a5632645/final_design/pctest/raylib/examples/audio/audio_mixed_processor.png

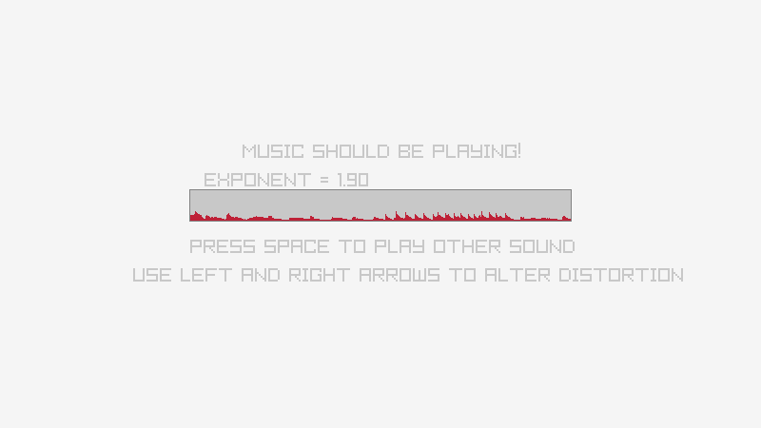
pctest/raylib/examples/audio/audio_mixed_processor.png
