a5632645/final_design/pctest/raylib/examples/audio/audio_stream_effects.png

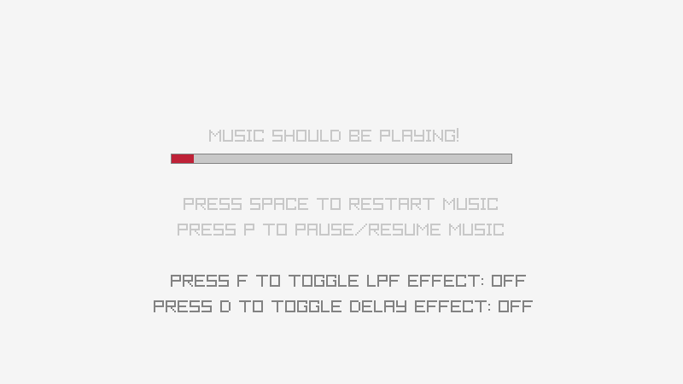
pctest/raylib/examples/audio/audio_stream_effects.png
