a5632645/final_design/pctest/raylib/examples/core/core_automation_events.png

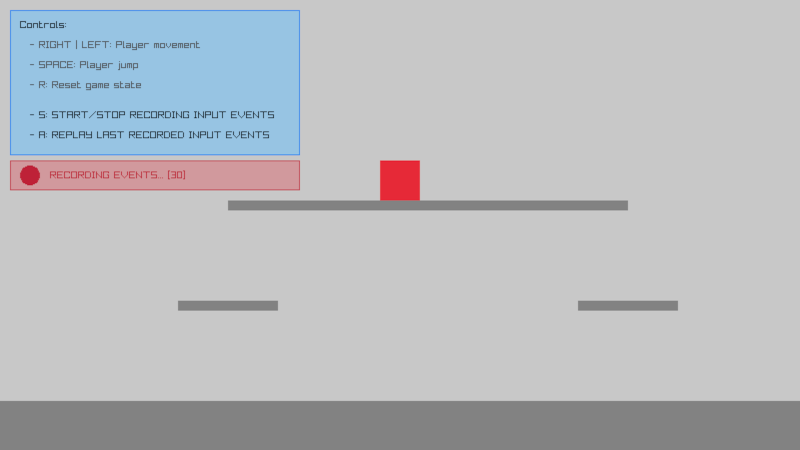
pctest/raylib/examples/core/core_automation_events.png
