a5632645/final_design/pctest/raylib/examples/core/core_input_gestures_web.png

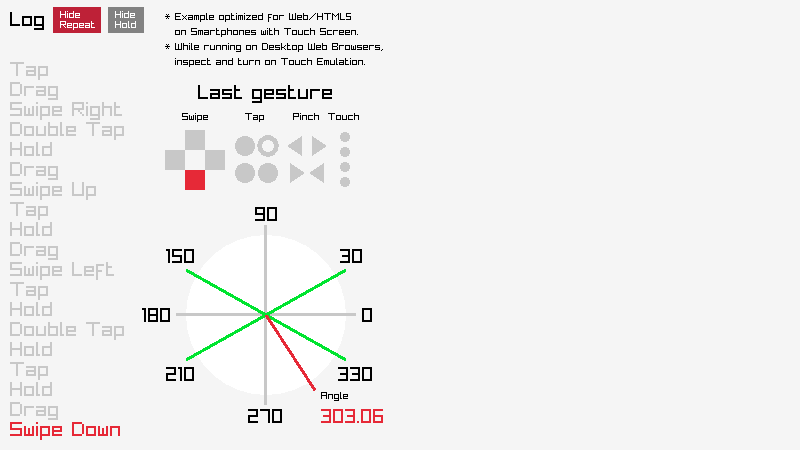
pctest/raylib/examples/core/core_input_gestures_web.png
