a5632645/final_design/pctest/raylib/examples/core/resources/ps3.png

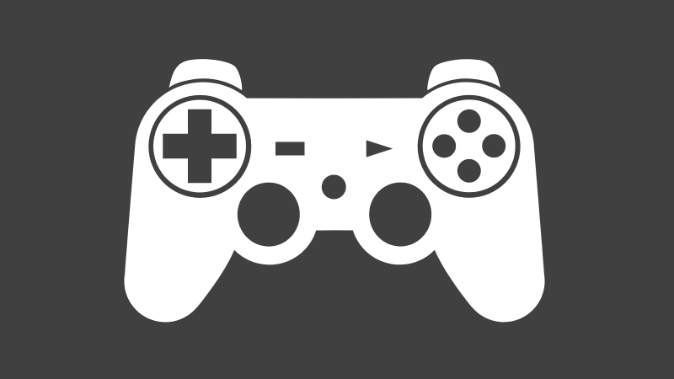
pctest/raylib/examples/core/resources/ps3.png
