a5632645/final_design/pctest/raylib/examples/core/resources/xbox.png

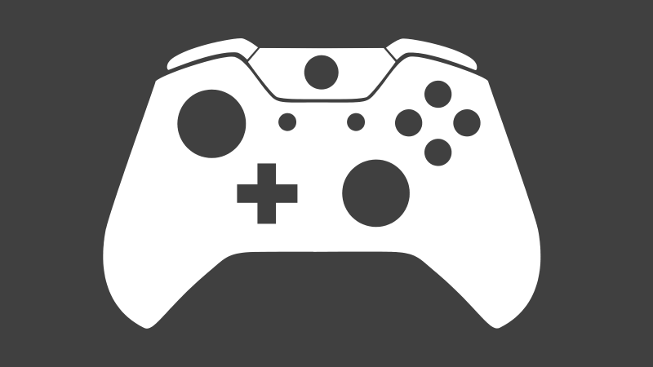
pctest/raylib/examples/core/resources/xbox.png
