a5632645/final_design/pctest/raylib/examples/models/models_bone_socket.png

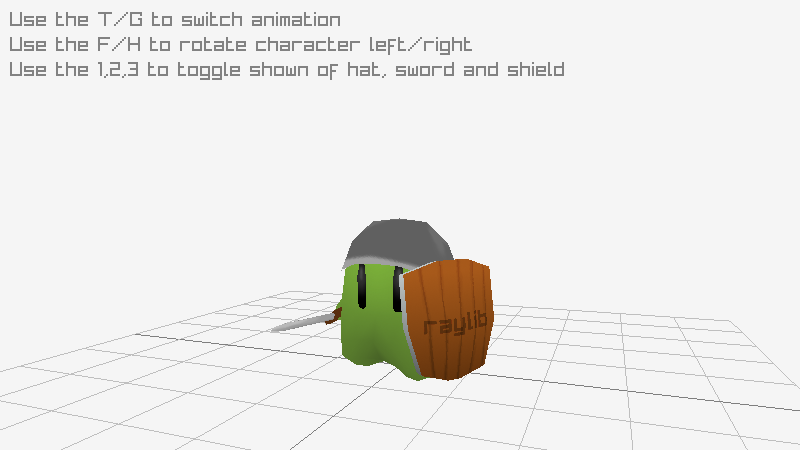
pctest/raylib/examples/models/models_bone_socket.png
