a5632645/final_design/pctest/raylib/examples/models/models_draw_cube_texture.png

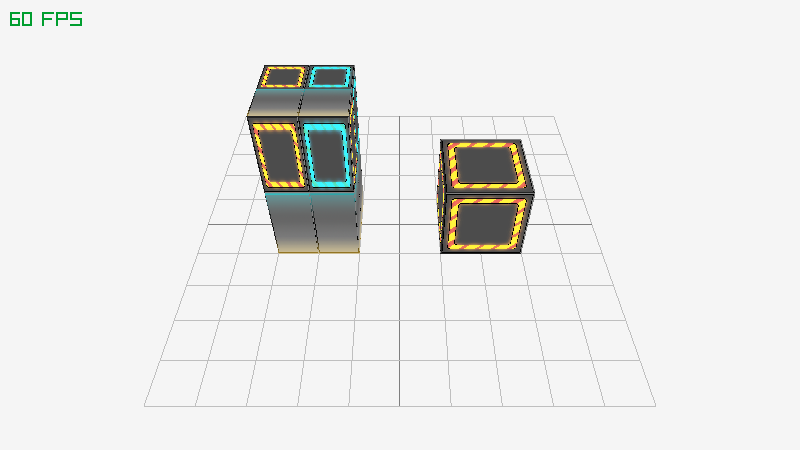
pctest/raylib/examples/models/models_draw_cube_texture.png
