a5632645/final_design/pctest/raylib/examples/models/resources/billboard.png

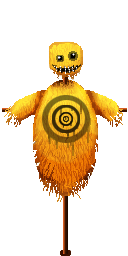
pctest/raylib/examples/models/resources/billboard.png
