a5632645/final_design/pctest/raylib/examples/models/resources/cubicmap_atlas.png

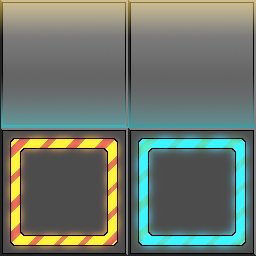
pctest/raylib/examples/models/resources/cubicmap_atlas.png
