a5632645/final_design/pctest/raylib/examples/models/resources/heightmap.png

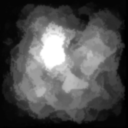
pctest/raylib/examples/models/resources/heightmap.png
