a5632645/final_design/pctest/raylib/examples/models/resources/models/iqm/guytex.png

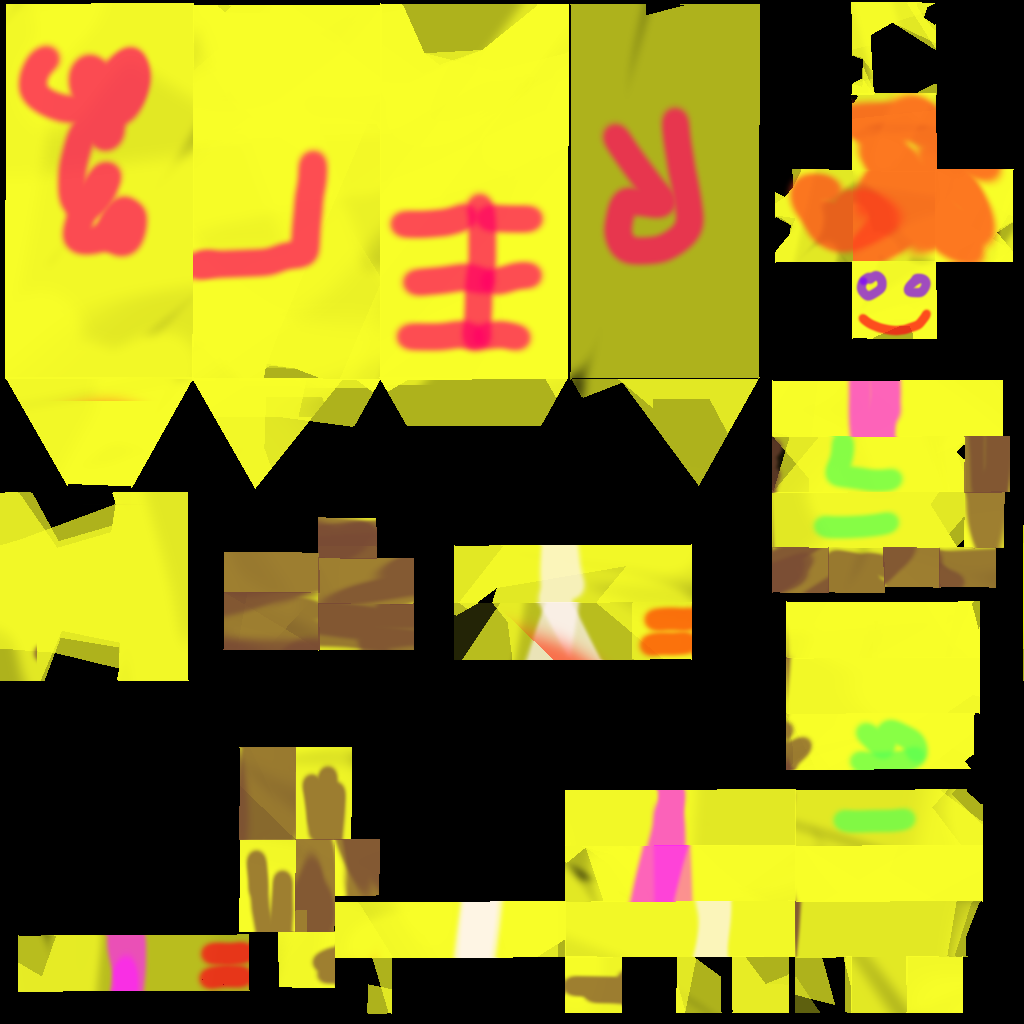
pctest/raylib/examples/models/resources/models/iqm/guytex.png
