a5632645/final_design/pctest/raylib/examples/models/resources/models/obj/castle_diffuse.png

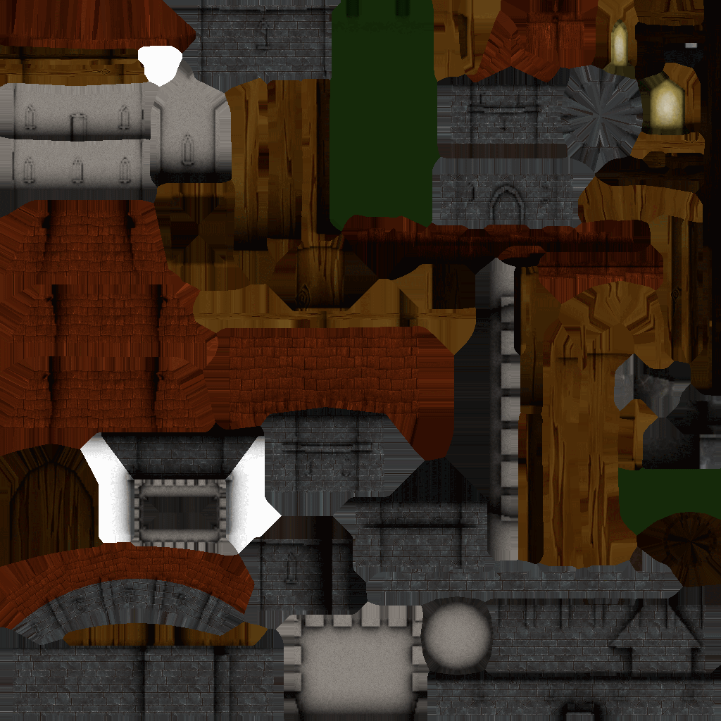
pctest/raylib/examples/models/resources/models/obj/castle_diffuse.png
