a5632645/final_design/pctest/raylib/examples/models/resources/models/obj/cube_diffuse.png

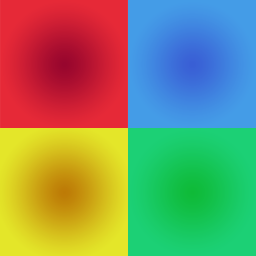
pctest/raylib/examples/models/resources/models/obj/cube_diffuse.png
