a5632645/final_design/pctest/raylib/examples/models/resources/models/obj/well_diffuse.png

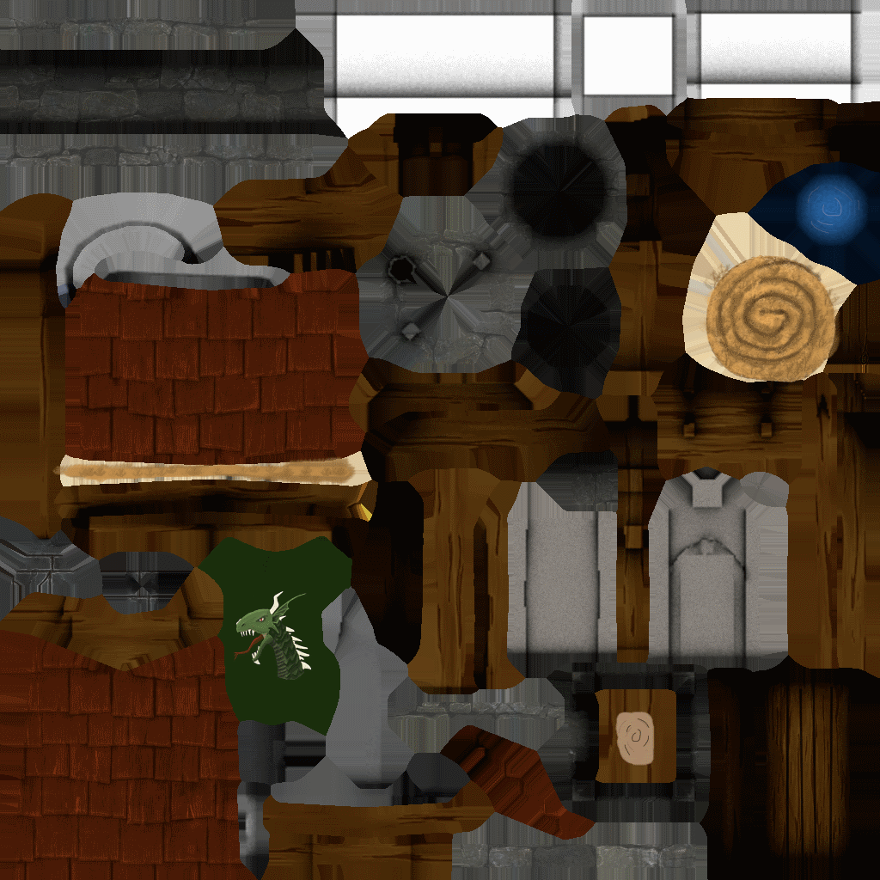
pctest/raylib/examples/models/resources/models/obj/well_diffuse.png
