a5632645/final_design/pctest/raylib/examples/models/resources/skybox.png

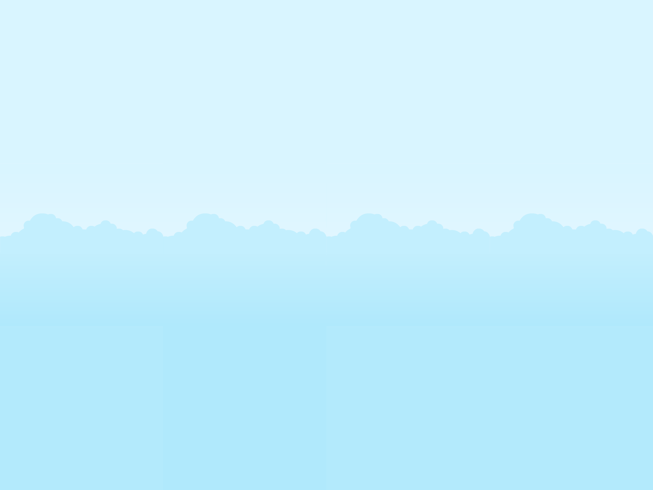
pctest/raylib/examples/models/resources/skybox.png
