a5632645/final_design/pctest/raylib/examples/others/raymath_vector_angle.png

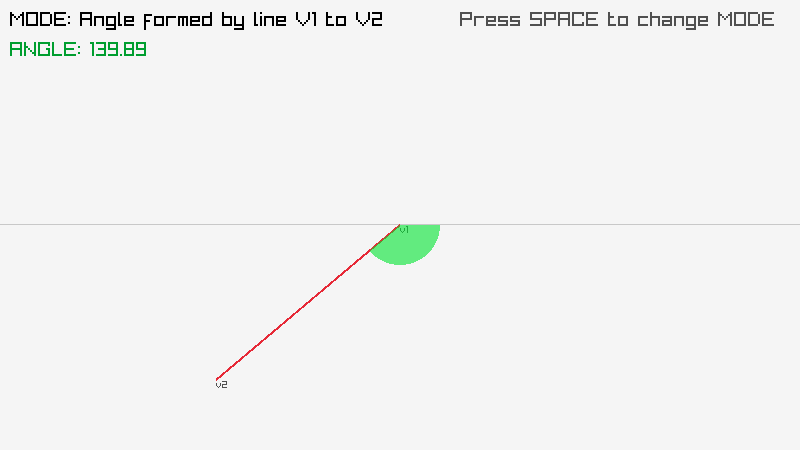
pctest/raylib/examples/others/raymath_vector_angle.png
