a5632645/final_design/pctest/raylib/examples/shaders/resources/fudesumi.png

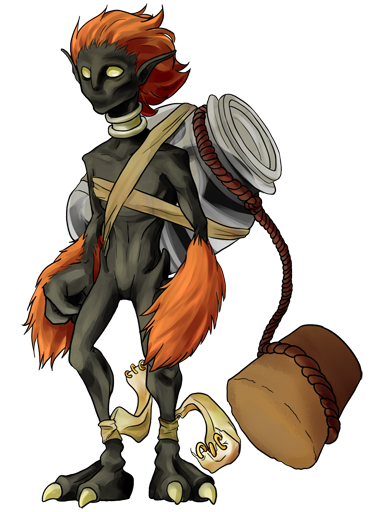
pctest/raylib/examples/shaders/resources/fudesumi.png
