a5632645/final_design/pctest/raylib/examples/shaders/resources/mask.png

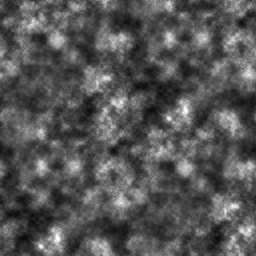
pctest/raylib/examples/shaders/resources/mask.png
