a5632645/final_design/pctest/raylib/examples/shaders/resources/models/barracks_diffuse.png

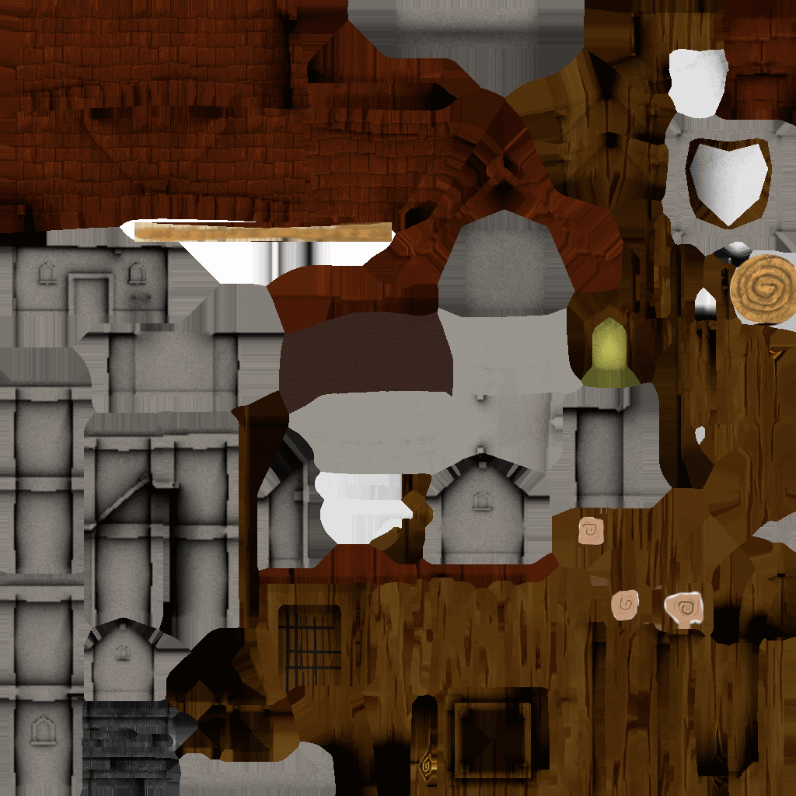
pctest/raylib/examples/shaders/resources/models/barracks_diffuse.png
