a5632645/final_design/pctest/raylib/examples/shaders/resources/models/watermill_diffuse.png

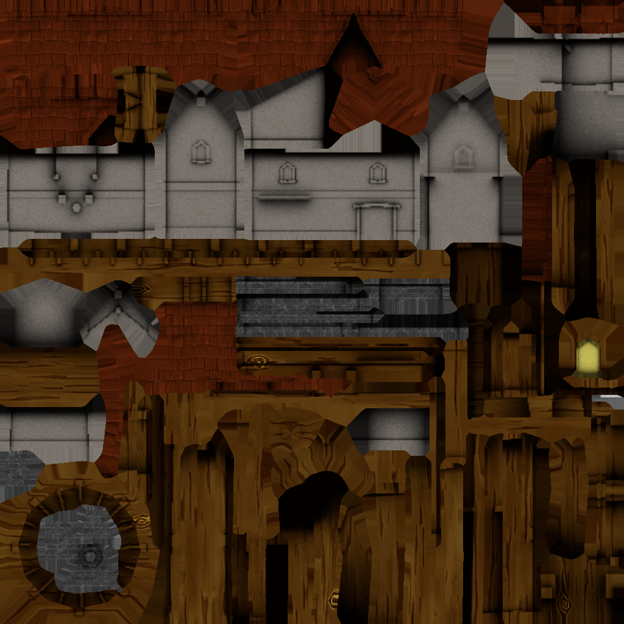
pctest/raylib/examples/shaders/resources/models/watermill_diffuse.png
