a5632645/final_design/pctest/raylib/examples/shaders/resources/plasma.png

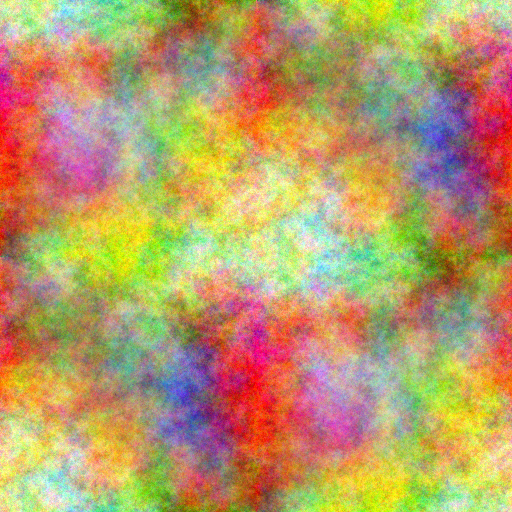
pctest/raylib/examples/shaders/resources/plasma.png
