a5632645/final_design/pctest/raylib/examples/shaders/resources/road_a.png

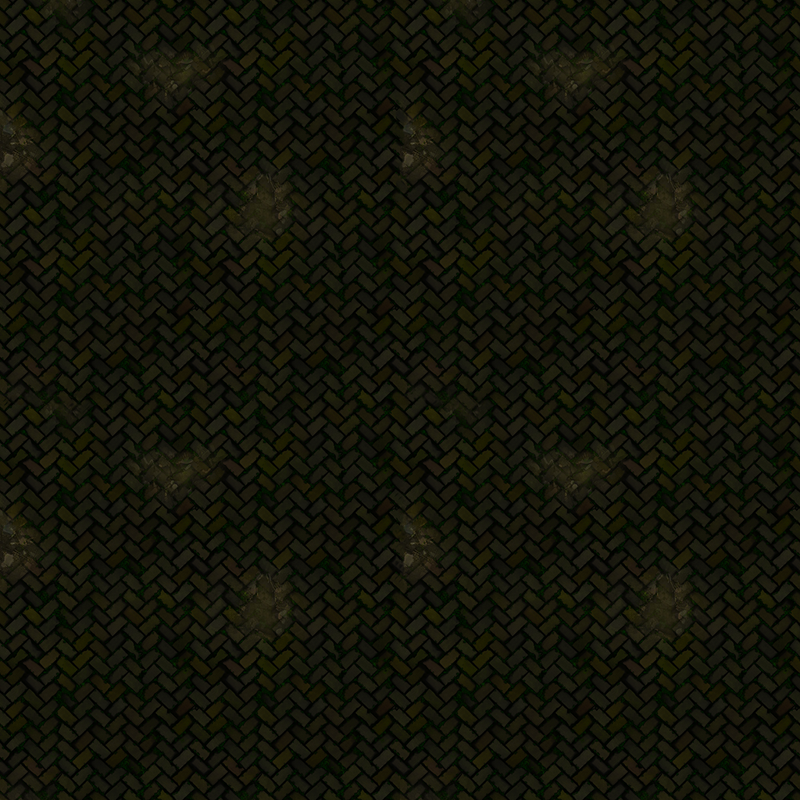
pctest/raylib/examples/shaders/resources/road_a.png
