a5632645/final_design/pctest/raylib/examples/shaders/resources/road_mra.png

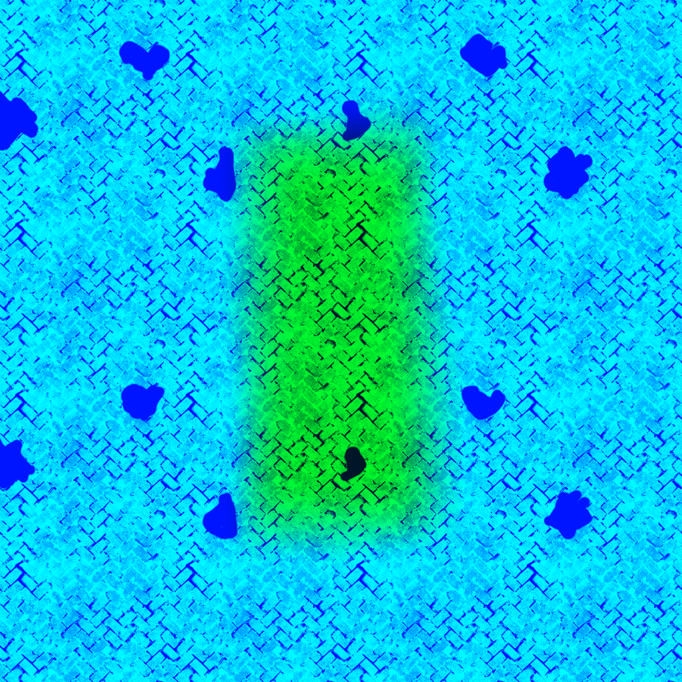
pctest/raylib/examples/shaders/resources/road_mra.png
