a5632645/final_design/pctest/raylib/examples/shaders/resources/road_n.png

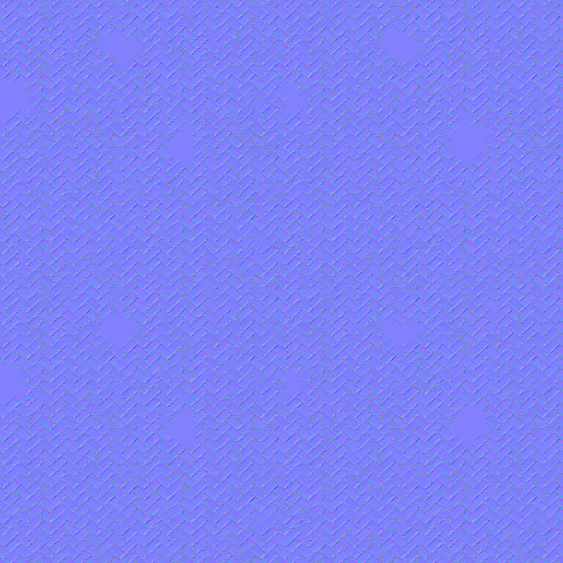
pctest/raylib/examples/shaders/resources/road_n.png
