a5632645/final_design/pctest/raylib/examples/shaders/resources/space.png

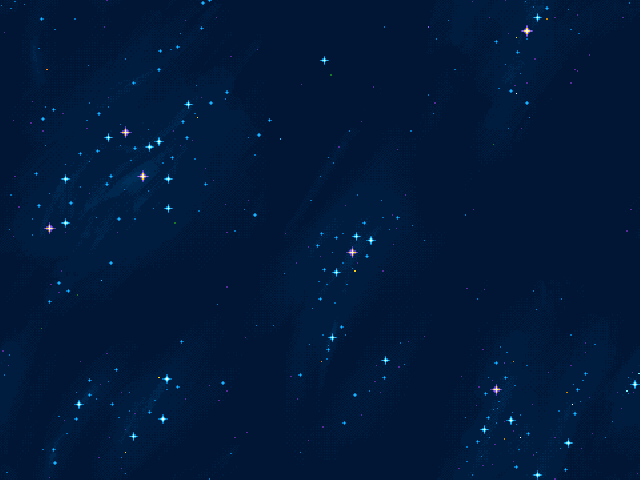
pctest/raylib/examples/shaders/resources/space.png
