a5632645/final_design/pctest/raylib/examples/shaders/resources/spark_flame.png

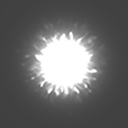
pctest/raylib/examples/shaders/resources/spark_flame.png
