a5632645/final_design/pctest/raylib/examples/shaders/resources/texel_checker.png

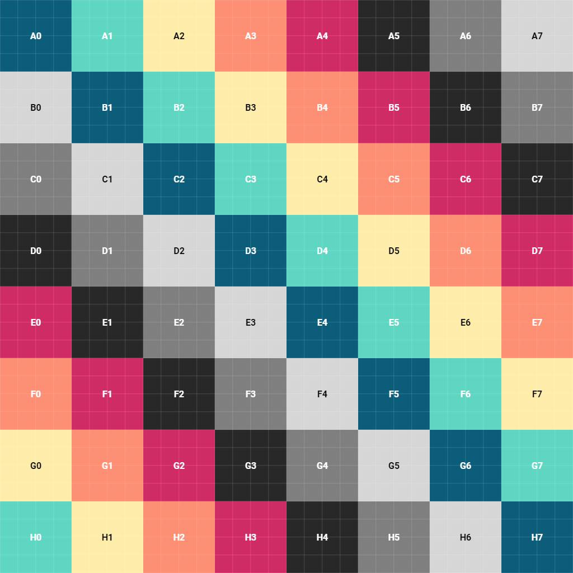
pctest/raylib/examples/shaders/resources/texel_checker.png
