a5632645/final_design/pctest/raylib/examples/shaders/shaders_basic_pbr.png

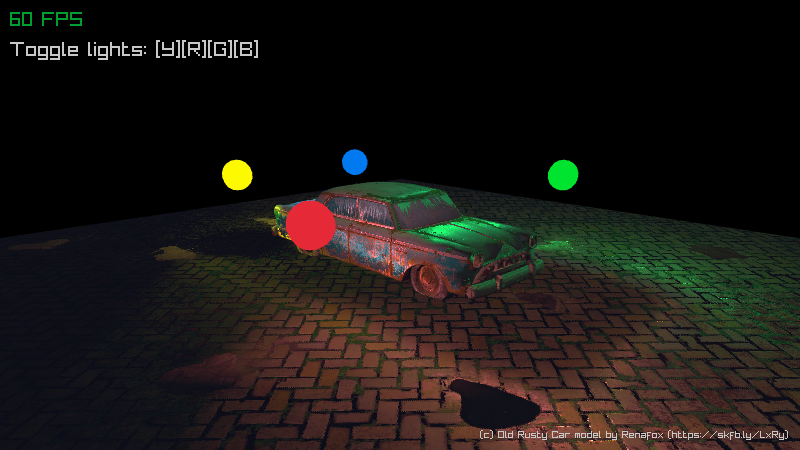
pctest/raylib/examples/shaders/shaders_basic_pbr.png
