a5632645/final_design/pctest/raylib/examples/shaders/shaders_hybrid_render.png

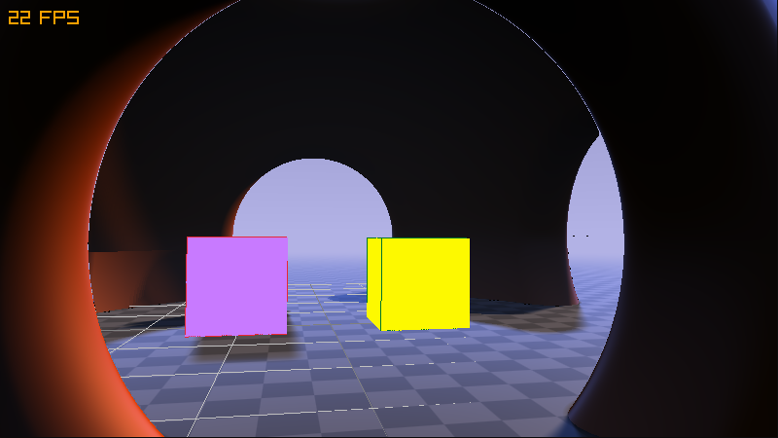
pctest/raylib/examples/shaders/shaders_hybrid_render.png
