a5632645/final_design/pctest/raylib/examples/shaders/shaders_lightmap.png

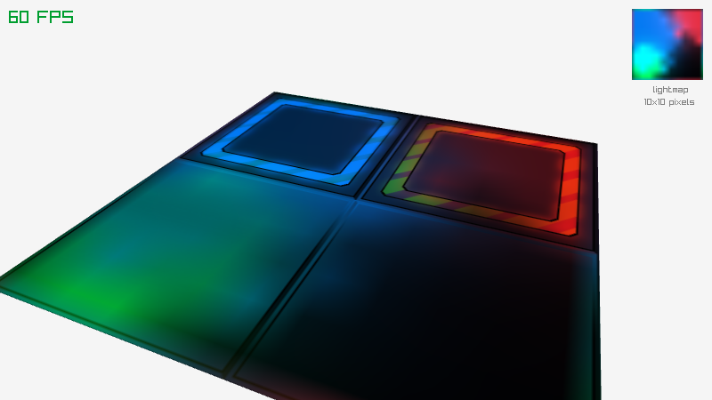
pctest/raylib/examples/shaders/shaders_lightmap.png
