a5632645/final_design/pctest/raylib/examples/shaders/shaders_shadowmap.png

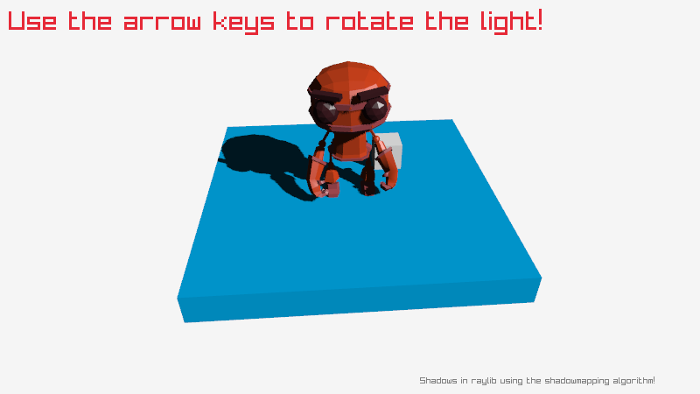
pctest/raylib/examples/shaders/shaders_shadowmap.png
