a5632645/final_design/pctest/raylib/examples/shaders/shaders_texture_tiling.png

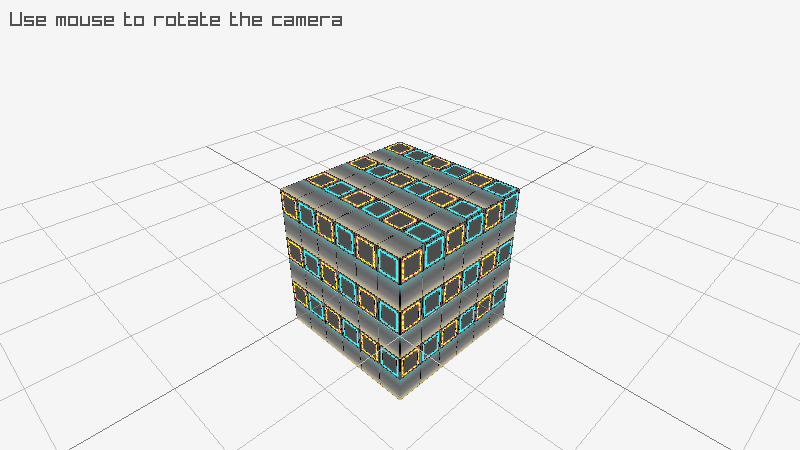
pctest/raylib/examples/shaders/shaders_texture_tiling.png
