a5632645/final_design/pctest/raylib/examples/shaders/shaders_vertex_displacement.png

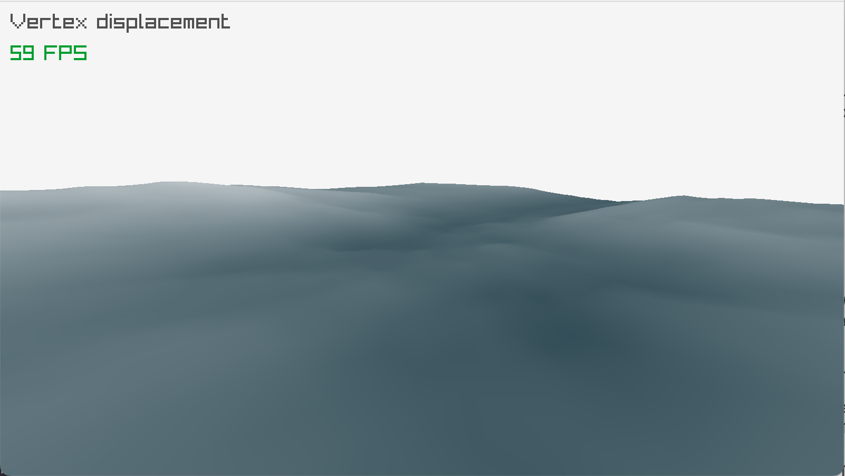
pctest/raylib/examples/shaders/shaders_vertex_displacement.png
