a5632645/final_design/pctest/raylib/examples/shaders/shaders_write_depth.png

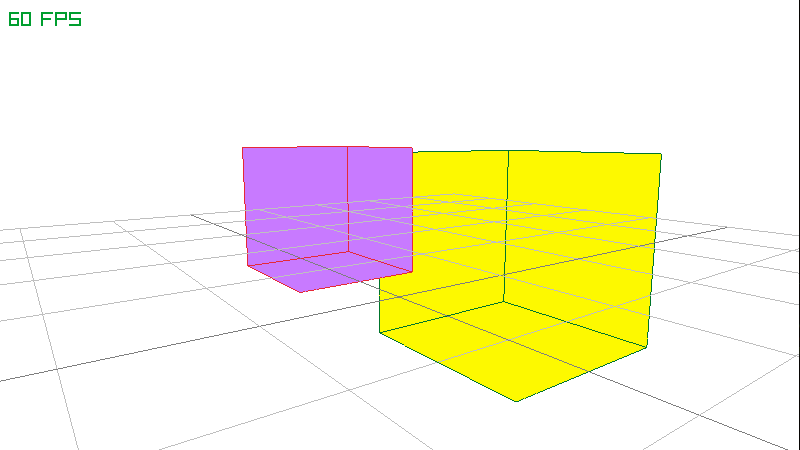
pctest/raylib/examples/shaders/shaders_write_depth.png
