a5632645/final_design/pctest/raylib/examples/shapes/shapes_splines_drawing.png

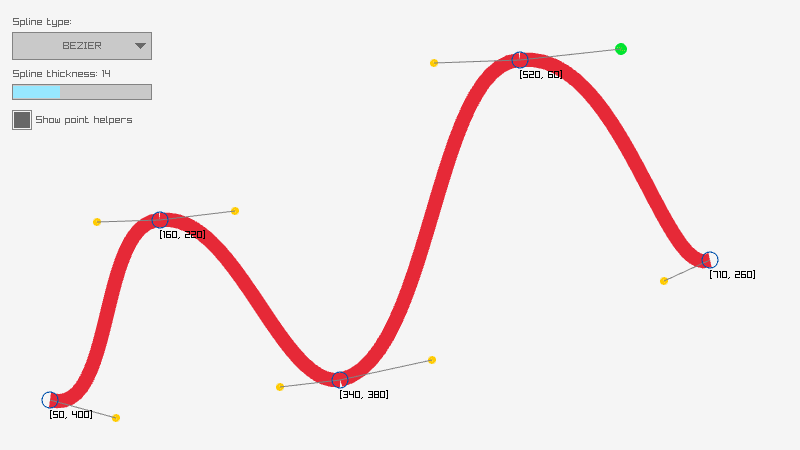
pctest/raylib/examples/shapes/shapes_splines_drawing.png
