a5632645/final_design/pctest/raylib/examples/text/resources/custom_alagard.png

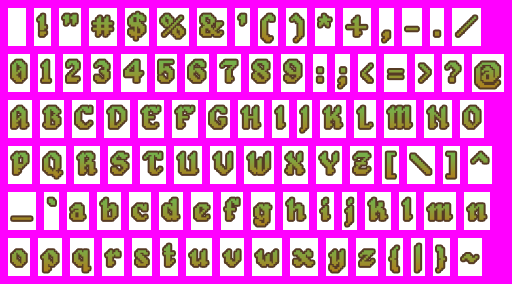
pctest/raylib/examples/text/resources/custom_alagard.png
