a5632645/final_design/pctest/raylib/examples/text/resources/custom_jupiter_crash.png

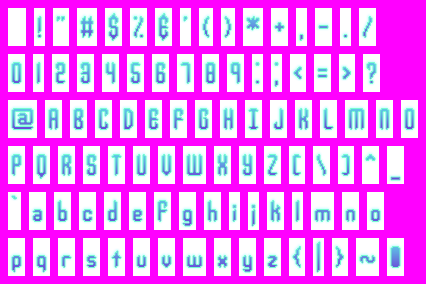
pctest/raylib/examples/text/resources/custom_jupiter_crash.png
