a5632645/final_design/pctest/raylib/examples/text/resources/custom_mecha.png

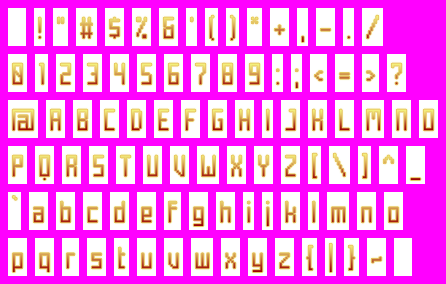
pctest/raylib/examples/text/resources/custom_mecha.png
