a5632645/final_design/pctest/raylib/examples/text/resources/dejavu.png

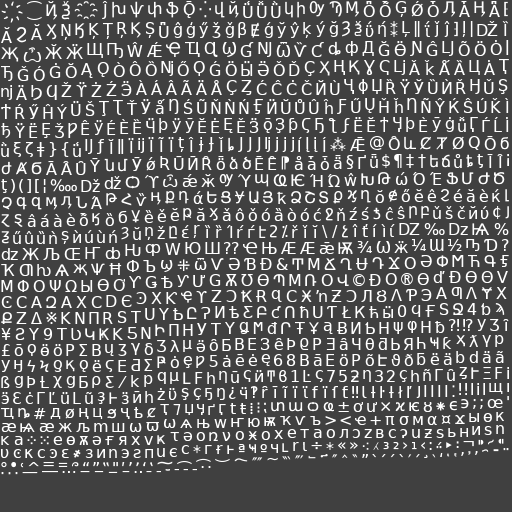
pctest/raylib/examples/text/resources/dejavu.png
