a5632645/final_design/pctest/raylib/examples/text/resources/fonts/alpha_beta.png

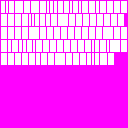
pctest/raylib/examples/text/resources/fonts/alpha_beta.png
