a5632645/final_design/pctest/raylib/examples/text/resources/fonts/jupiter_crash.png

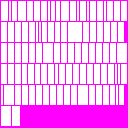
pctest/raylib/examples/text/resources/fonts/jupiter_crash.png
