a5632645/final_design/pctest/raylib/examples/text/resources/fonts/mecha.png

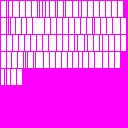
pctest/raylib/examples/text/resources/fonts/mecha.png
