a5632645/final_design/pctest/raylib/examples/text/resources/fonts/pixantiqua.png

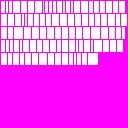
pctest/raylib/examples/text/resources/fonts/pixantiqua.png
