a5632645/final_design/pctest/raylib/examples/text/resources/fonts/pixelplay.png

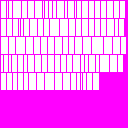
pctest/raylib/examples/text/resources/fonts/pixelplay.png
