a5632645/final_design/pctest/raylib/examples/text/resources/fonts/setback.png

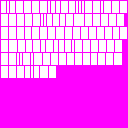
pctest/raylib/examples/text/resources/fonts/setback.png
