a5632645/final_design/pctest/raylib/examples/text/resources/noto_cjk.png

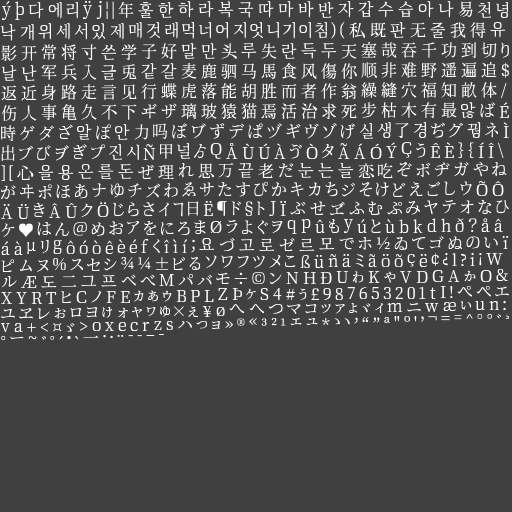
pctest/raylib/examples/text/resources/noto_cjk.png
