a5632645/final_design/pctest/raylib/examples/text/resources/pixantiqua.png

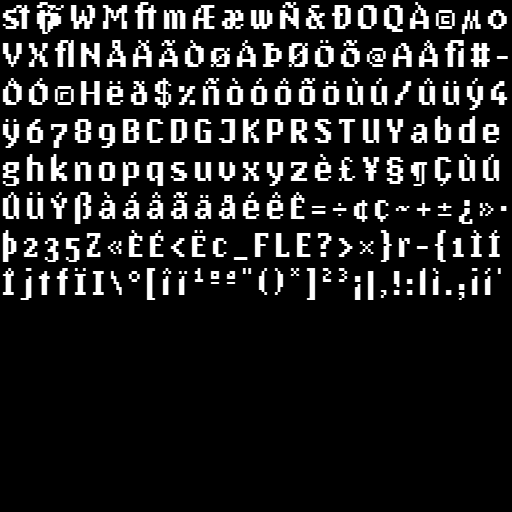
pctest/raylib/examples/text/resources/pixantiqua.png
