a5632645/final_design/pctest/raylib/examples/text/resources/symbola.png

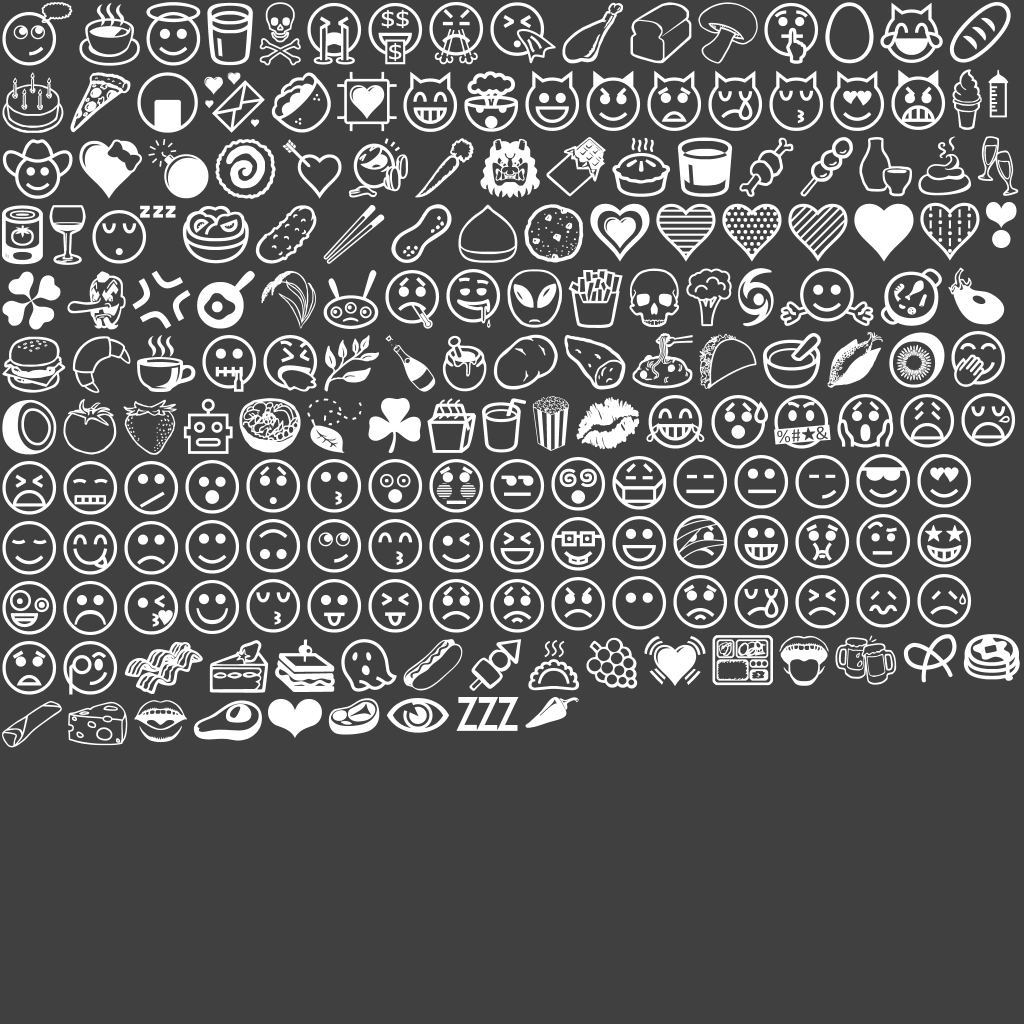
pctest/raylib/examples/text/resources/symbola.png
