a5632645/final_design/pctest/raylib/examples/textures/resources/button.png

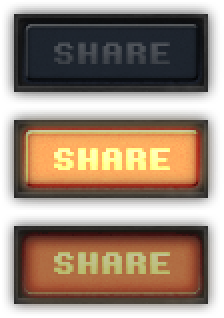
pctest/raylib/examples/textures/resources/button.png
