a5632645/final_design/pctest/raylib/examples/textures/resources/cat.png

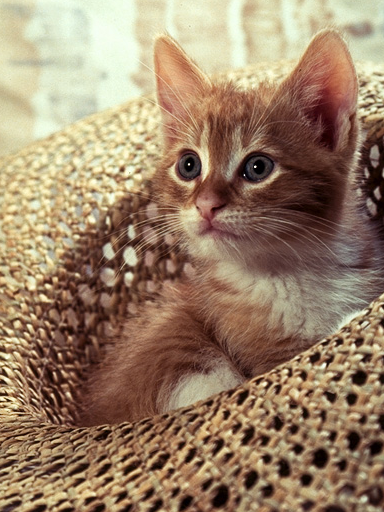
pctest/raylib/examples/textures/resources/cat.png
