a5632645/final_design/pctest/raylib/examples/textures/resources/cyberpunk_street_background.png

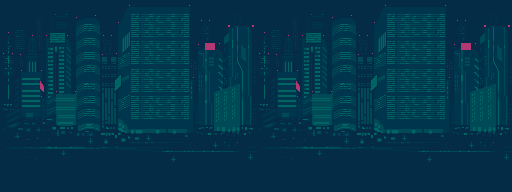
pctest/raylib/examples/textures/resources/cyberpunk_street_background.png
