a5632645/final_design/pctest/raylib/examples/textures/resources/cyberpunk_street_midground.png

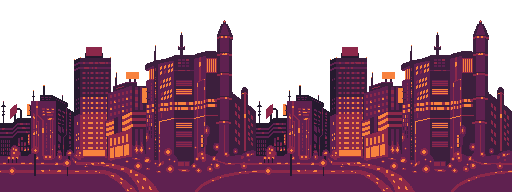
pctest/raylib/examples/textures/resources/cyberpunk_street_midground.png
