a5632645/final_design/pctest/raylib/examples/textures/resources/explosion.png

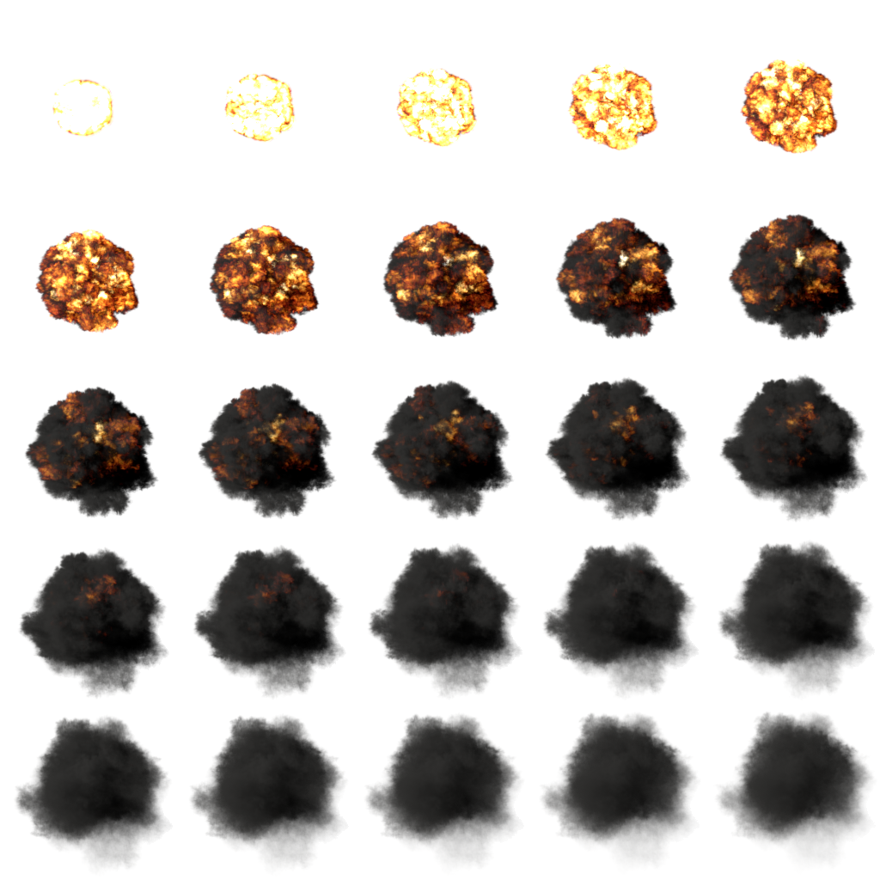
pctest/raylib/examples/textures/resources/explosion.png
