a5632645/final_design/pctest/raylib/examples/textures/resources/parrots.png

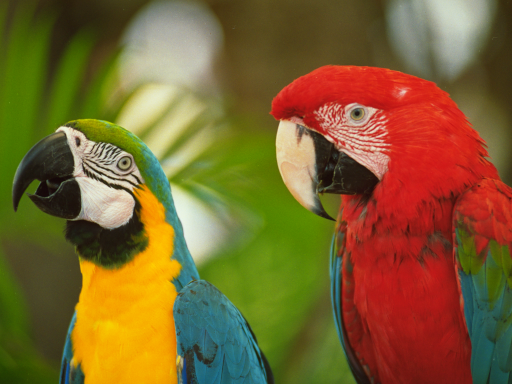
pctest/raylib/examples/textures/resources/parrots.png
