a5632645/final_design/pctest/raylib/examples/textures/resources/patterns.png

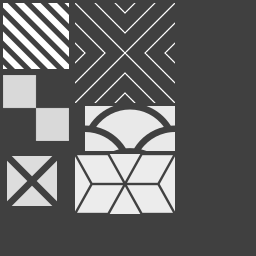
pctest/raylib/examples/textures/resources/patterns.png
