a5632645/final_design/pctest/raylib/examples/textures/resources/scarfy_run.gif

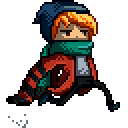
pctest/raylib/examples/textures/resources/scarfy_run.gif
