a5632645/final_design/pctest/raylib/examples/textures/textures_image_rotate.png

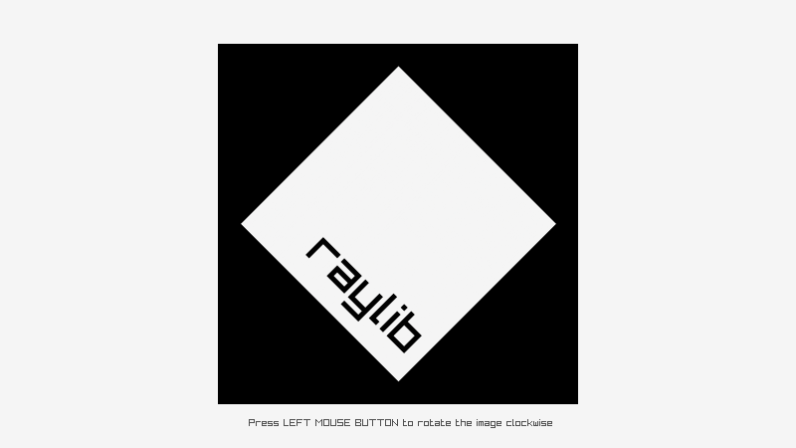
pctest/raylib/examples/textures/textures_image_rotate.png
