a5632645/final_design/pctest/raylib/examples/textures/textures_textured_curve.png

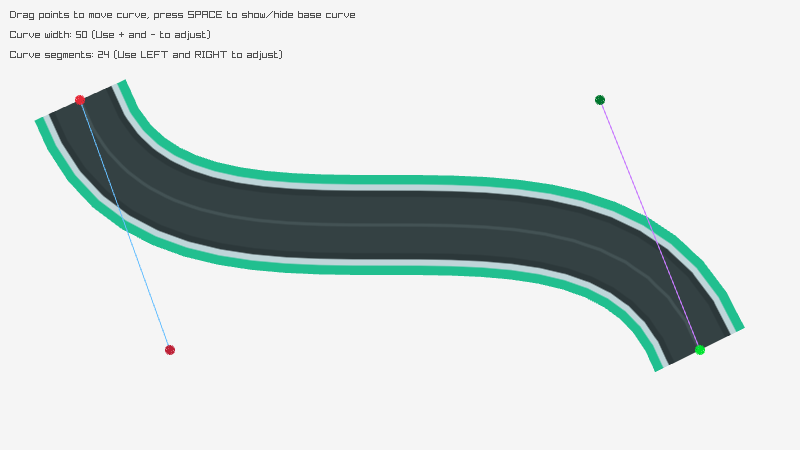
pctest/raylib/examples/textures/textures_textured_curve.png
