a5632645/final_design/WaveGuideSoft/CMSIS-DSP-1.16.2/Documentation/Doxygen/src/images/CFFT_Radix2.gif

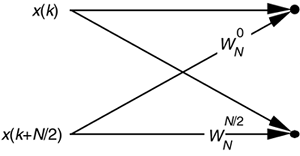
WaveGuideSoft/CMSIS-DSP-1.16.2/Documentation/Doxygen/src/images/CFFT_Radix2.gif
