a5632645/final_design/WaveGuideSoft/Waveguide/dsp/Body.cpp

#include "Body.hpp"
#include "AudioFFT.h"
#include <numbers>
#include <cmath>
#include "utli/Lerp.hpp"
#include "MemAttributes.hpp"

constexpr float kBanjo[4096] = {0.8408116, -0.2511731, -0.38303635, -0.0059898444, -0.27061847, 0.0007890034, -0.0073292973, 0.011994778, -0.012411621, 0.04655279, 0.056455344, 0.014067898, 0.07330127, -0.05343846, 0.028716885, -0.010607676, 0.0015999887, 0.043362975, -0.032687552, 0.0154145565, 0.062117293, 0.025567032, -0.08403967, 0.0062902574, 0.010043268, -0.051865425, 0.033150233, 0.020506015, -0.0044696927, 0.04990088, 0.03276305, -0.04390349, -0.02187753, -0.046611894, -0.07722027, -0.027850313, 0.01636171, 0.0030558843, -0.032876786, -0.036291096, -0.09235733, -0.087776974, -0.03540004, -0.04335503, -0.0653021, -0.044091616, -0.107368715, -0.19948685, -0.12446984, -0.12928312, -0.17091624, -0.15268704, -0.16255362, -0.12987855, -0.069635436, -0.060110703, -0.1134893, -0.11407602, -0.12384962, -0.09637414, -0.044933986, -0.07018676, -0.036956374, -0.034364752, -0.018860595, 0.025873553, 0.02347859, 0.0366431, 0.016929181, 0.038740564, 0.094063744, 0.10979407, 0.07708771, 0.040532988, 0.055806838, 0.06596992, 0.08629575, 0.13908072, 0.21054052, 0.19513358, 0.1566528, 0.15990843, 0.11960288, 0.16314034, 0.22333363, 0.2422042, 0.2616581, 0.27669352, 0.31851187, 0.29176015, 0.22406402, 0.15822846, 0.1264795, 0.12470437, 0.11616462, 0.10107283, 0.073159724, 0.1277734, 0.175093, 0.14201444, 0.07894555, 0.023511363, 0.012008642, -0.015200933, -0.030257491, -0.047351334, -0.07098553, -0.05507381, -0.0735658, -0.12708904, -0.17628899, -0.20585562, -0.21016774, -0.21126585, -0.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
