a5632645/final_design/WaveGuideSoft/Waveguide/bsp/ST7735S.hpp

#pragma once
#include <cstdint>
#include <span>
#include "oled/OLEDDisplay.h"

namespace bsp {

class CUC1638 {
public:
    void Init();
    void UpdateScreen();

    void SetBKlight(bool on);
    void SetMirror(bool x, bool y);

    void HardReset();
    void PowerUpSequence();

    void _WriteCommand(uint8_t cmd);
    void _WriteData(uint8_t data);
    void WriteAddress(uint16_t address1, uint16_t address2);
    void WriteDataSpan(std::span<uint8_t> data);
    
    OLEDDisplay display;
    bool xMirror_{ true };
    bool yMirror_{ false };
private:
    void _DC(bool on);
    void _CS(bool on);
};

namespace internal {
struct InternalUC1638 {
    inline static CUC1638 instance;
};
}

inline static auto& UC1638 = internal::InternalUC1638::instance;

}
